pablozg/freeds/include/bitmap.h

// 'FreeDS - copia', 128x64px
const unsigned char FreeDS[] = {
  0x00, 0x00, 0x00, 0x00, 0x00, 0x00, 0x00, 0x00, 0x00, 0x00, 0x00, 0x00, 
  0x00, 0x00, 0x00, 0x00, 0x00, 0x00, 0x00, 0x00, 0x00, 0x00, 0x00, 0x00, 
  0x00, 0x00, 0x00, 0x00, 0x30, 0x00, 0x00, 0x00, 0x00, 0x00, 0x00, 0x00, 
  0xFF, 0x00, 0x00, 0x00, 0x00, 0x00, 0x00, 0xF0, 0xE0, 0x01, 0x00, 0x00, 
  0x00, 0x00, 0x00, 0x0F, 0xE0, 0x01, 0x00, 0x00, 0x00, 0x00, 0xF0, 0x09, 
  0xE0, 0x01, 0x00, 0x00, 0x00, 0x00, 0x1F, 0x08, 0xE0, 0x01, 0x00, 0x00, 
  0x00, 0xF0, 0x03, 0x08, 0xE0, 0x01, 0x00, 0x00, 0x00, 0x1F, 0x02, 0x08, 
  0xE0, 0x01, 0x00, 0x00, 0xC0, 0x01, 0x02, 0x08, 0xE0, 0x01, 0x00, 0x00, 
  0xC0, 0x00, 0x02, 0x08, 0xE0, 0x01, 0x00, 0x00, 0xC0, 0x00, 0x02, 0x08, 
  0xF0, 0x01, 0x80, 0x00, 0xC0, 0x00, 0x02, 0x08, 0xFE, 0x01, 0x80, 0x00, 
  0xC0, 0x00, 0x02, 0xE8, 0xE1, 0x01, 0x80, 0x00, 0xC0, 0x00, 0x02, 0x1E, 
  0xE0, 0x01, 0x80, 0x00, 0xC0, 0x00, 0xE2, 0x0B, 0xE0, 0x01, 0x80, 0x00, 
  0xC0, 0x00, 0x3F, 0x08, 0xE0, 0x01, 0x80, 0x00, 0xC0, 0xE0, 0x03, 0x08, 
  0xE0, 0x01, 0x80, 0x00, 0xC0, 0x3C, 0x02, 0x08, 0xE0, 0x01, 0x80, 0x00, 
  0xC0, 0x03, 0x02, 0x08, 0xE0, 0x01, 0x80, 0x00, 0xC0, 0x00, 0x02, 0x08, 
  0xE0, 0x01, 0x80, 0x00, 0xC0, 0x00, 0x02, 0x08, 0xE0, 0xFF, 0xFF, 0x00, 
  0xC0, 0x00, 0x02, 0x08, 0xFC, 0x01, 0x80, 0x00, 0xC0, 0x00, 0x02, 0xC8, 
  0xE3, 0x01, 0x80, 0x00, 0xC0, 0x00, 0x02, 0x3C, 0xE0, 0x01, 0x80, 0x00, 
  0xC0, 0x00, 0xC2, 0x0F, 0xE0, 0x01, 0x80, 0x00, 0xC0, 0x00, 0x7E, 0x08, 
  0xE0, 0xFF, 0xFF, 0x00, 0xC0, 0x80, 0x07, 0x08, 0xE0, 0x01, 0x80, 0x00, 
  0xC0, 0x7C, 0x03, 0x08, 0xE0, 0x01, 0x80, 0x00, 0xC0, 0x07, 0x02, 0x08, 
  0xE0, 0x01, 0x80, 0x00, 0xC0, 0x00, 0x02, 0x08, 0xE0, 0x01, 0x80, 0x00, 
  0xC0, 0x00, 0x02, 0x08, 0xE0, 0x01, 0x80, 0x00, 0xC0, 0x00, 0x02, 0x08, 
  0xF8, 0x01, 0x80, 0x00, 0xC0, 0x00, 0x02, 0x88, 0xE7, 0x01, 0x80, 0x00, 
  0xC0, 0x00, 0x02, 0xF8, 0xE0, 0x01, 0x80, 0x00, 0xC0, 0x00, 0x83, 0x0F, 
  0xE0, 0x01, 0x80, 0x00, 0xC0, 0x00, 0xF2, 0x08, 0xE0, 0x01, 0x80, 0x00, 
  0xC0, 0x80, 0x0F, 0x08, 0xE0, 0x01, 0x00, 0x00, 0xC0, 0xF0, 0x03, 0x08, 
  0xE0, 0x01, 0x00, 0x00, 0xC0, 0x0F, 0x02, 0x08, 0xE0, 0x01, 0x00, 0x00, 
  0xC0, 0x00, 0x02, 0x08, 0xE0, 0x01, 0x00, 0x00, 0xC0, 0x00, 0x02, 0x08, 
  0xE0, 0x01, 0x00, 0x00, 0xC0, 0x00, 0x02, 0x08, 0xF0, 0x01, 0x00, 0x00, 
  0xC0, 0x00, 0x02, 0x08, 0xFF, 0x01, 0x00, 0x00, 0xC0, 0x00, 0x02, 0xF8, 
  0xFF, 0x01, 0x00, 0x00, 0xC0, 0x00, 0x02, 0xFF, 0x7F, 0x00, 0x00, 0x00, 
  0xC0, 0x00, 0xE2, 0xFF, 0x0F, 0x00, 0x00, 0x00, 0xC0, 0x00, 0xFF, 0xFF, 
  0x00, 0x00, 0x00, 0x00, 0xC0, 0xE0, 0xFF, 0x0F, 0x00, 0x00, 0x00, 0x00, 
  0xC0, 0xFE, 0xFF, 0x00, 0x00, 0x00, 0x00, 0x00, 0x80, 0xFF, 0x0F, 0x00, 
  0x00, 0x00, 0x00, 0x00, 0x80, 0xFF, 0x00, 0x00, 0x00, 0x00, 0x00, 0x00, 
  0x00, 0x0E, 0x00, 0x00, 0x00, 0x00, 0x00, 0x00, 0x00, 0x00, 0x00, 0x00, 
  0x00, 0x00, 0x00, 0x00, 0x00, 0x00, 0x00, 0x00, 0x00, 0x00, 0x00, 0x00, 
  0x00, 0x00, 0x00, 0x00, 0x00, 0x00, 0x00, 0x00, 0x00, 0x00, 0x00, 0x00, 
  0x00, 0x00, 0x00, 0x00, 0x00, 0x00, 0x00, 0x00, 0x00, 0x00, 0x00, 0x00, 
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
